fpgirard/ratar/pcb/RF-HAT/RF-HAT.kicad_sch

## KiCad design pcb/RF-HAT/RF-HAT.kicad_sch (2026-08-22)

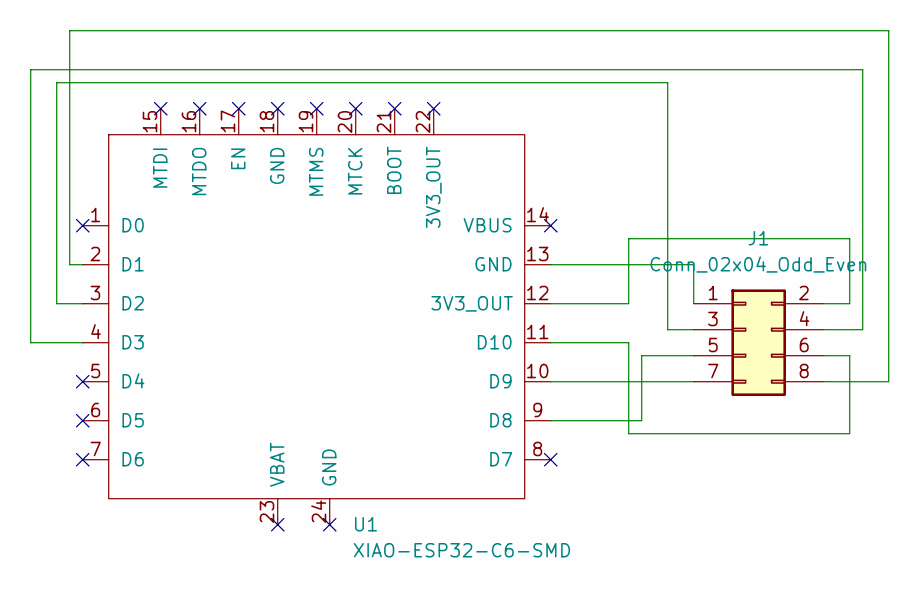
[picture p3: schematic RF-HAT.kicad_sch]

Parts:
J1: Conn_02x04_Odd_Even; PinSocket_2x04_P2.54mm_Vertical
U1: XIAO-ESP32-C6-SMD; XIAO-ESP32-C6-DIP

Connections:
unnamed: J1.1, U1.13 (GND)
unnamed: J1.2, U1.12 (3V3_OUT)
unnamed: J1.3, U1.3 (D2)
unnamed: J1.4, U1.4 (D3)
unnamed: J1.5, U1.9 (D8)
unnamed: J1.6, U1.11 (D10)
unnamed: J1.7, U1.10 (D9)
unnamed: J1.8, U1.2 (D1)
